v9938/MSX2SlotExpander/Image8.jpg

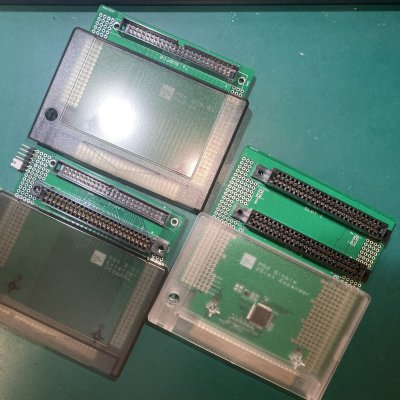
Image8.jpg
