v9938/MSX2SlotExpander/IMG_0485.JPG

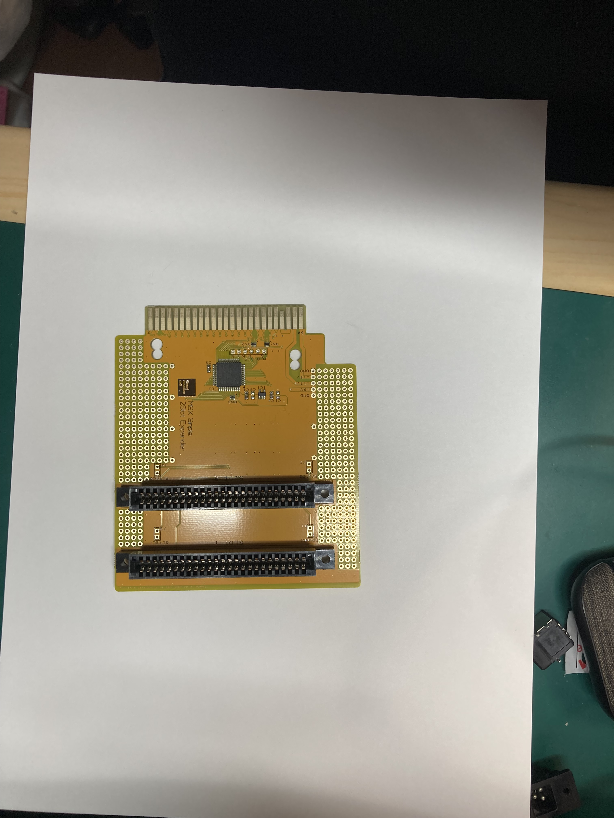
IMG_0485.JPG
